der-pw/HM-LC-Sw1-Pl-DN-R1_S26/img/PCB_3D_back.jpg

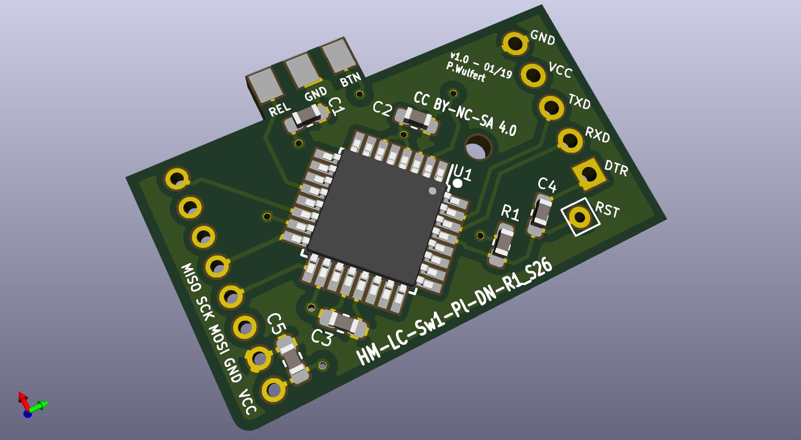
img/PCB_3D_back.jpg
