der-pw/HM-LC-Sw1-Pl-DN-R1_S26/img/S26_HM_eingeb_a.jpg

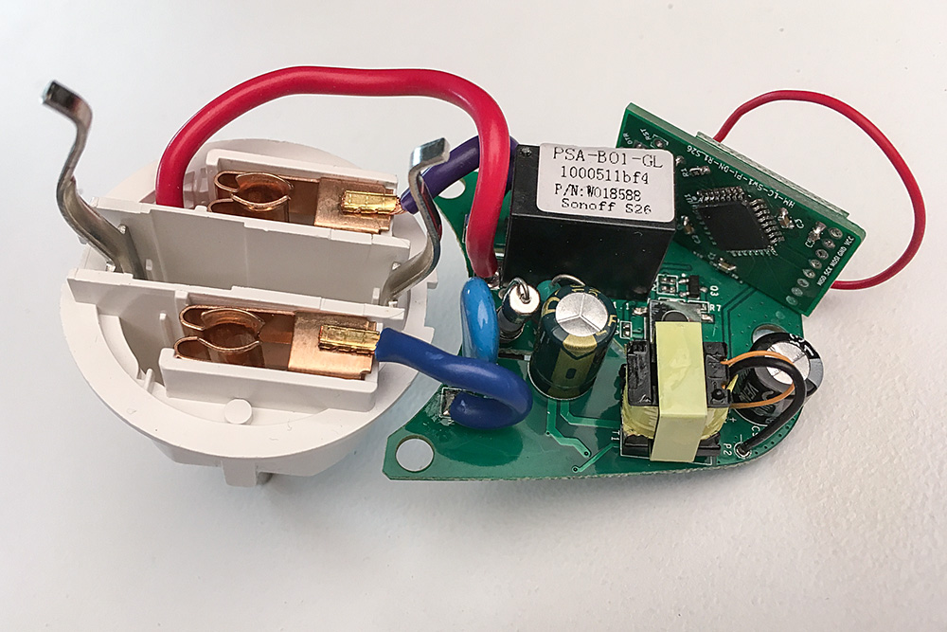
img/S26_HM_eingeb_a.jpg
