der-pw/HM-LC-Sw1-Pl-DN-R1_S26/img/S26_HM_front.jpg

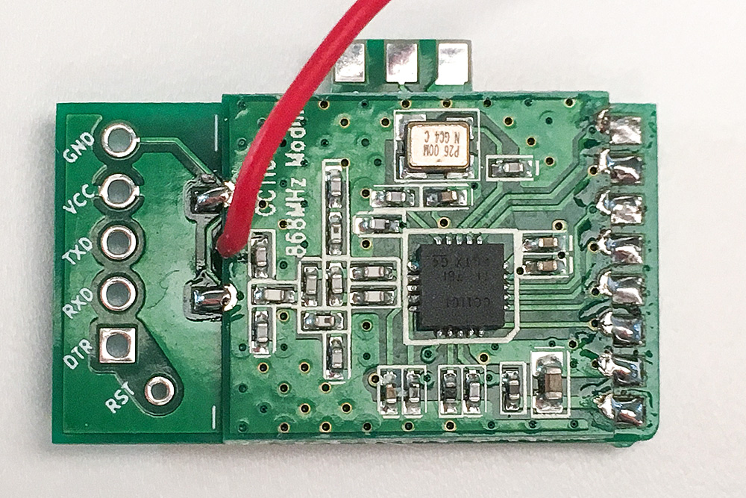
img/S26_HM_front.jpg
