der-pw/HM-LC-Sw1-Pl-DN-R1_S26/img/vergl_b.jpg

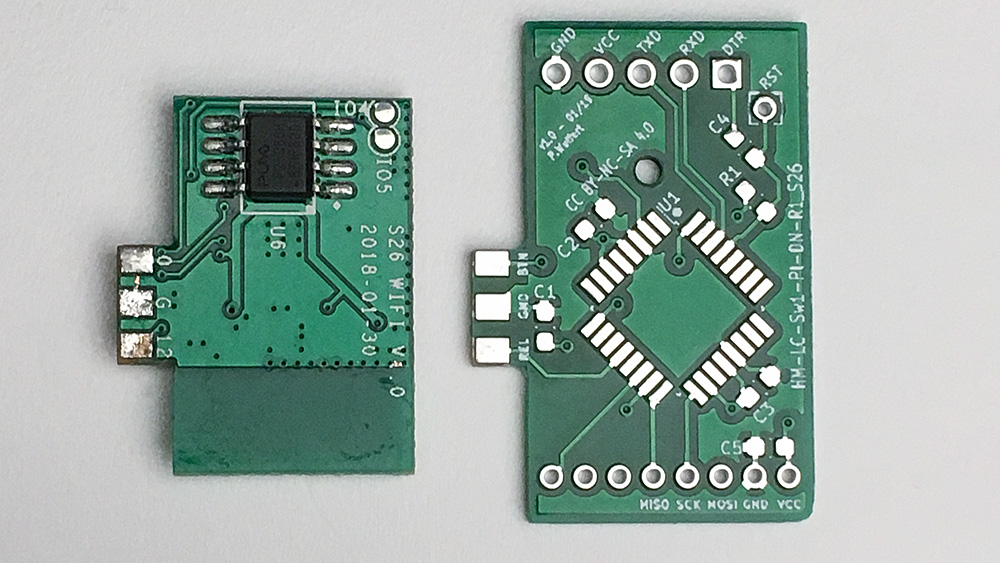
img/vergl_b.jpg
